analoghifi/HQ-Sub/docs/german uncorrected/SUBS-0.png

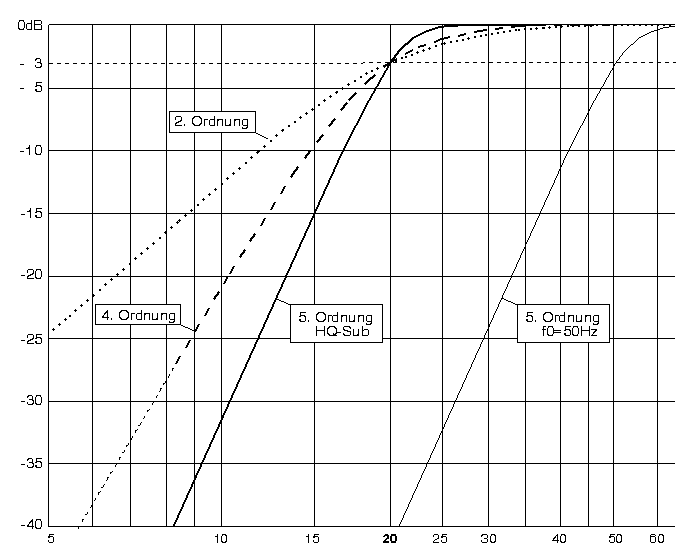
docs/german uncorrected/SUBS-0.png
