analoghifi/HQ-Sub/docs/german uncorrected/SUBS-10.png

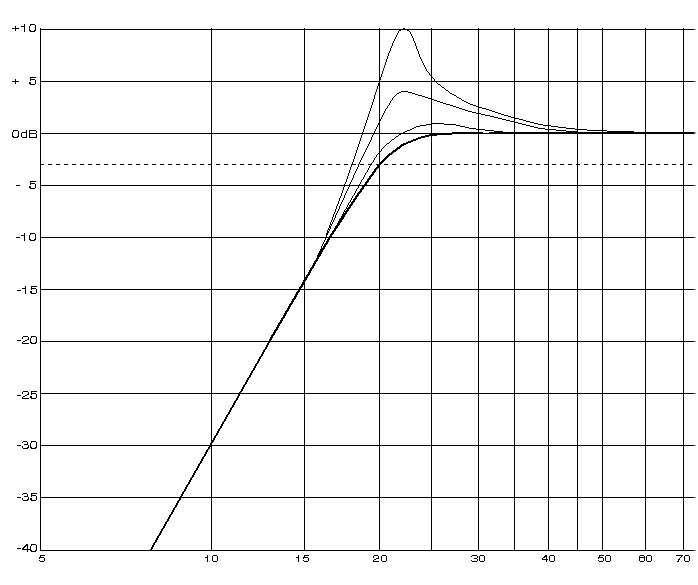
docs/german uncorrected/SUBS-10.png
