analoghifi/HQ-Sub/hardware/HQ-Sub_bottom.jpg

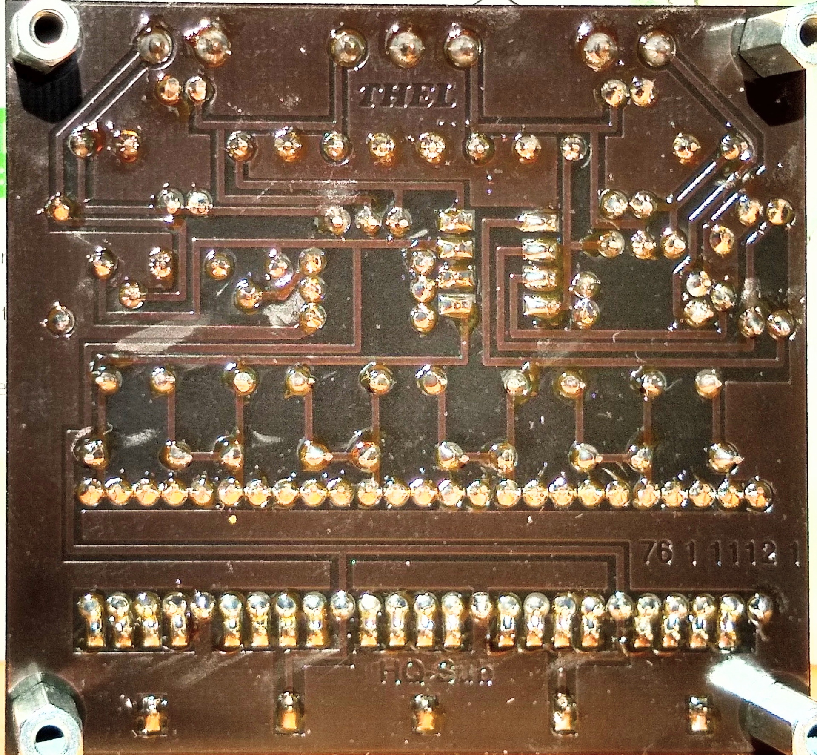
hardware/HQ-Sub_bottom.jpg
