analoghifi/HQ-Sub/hardware/HQ-Sub_Top (2).jpg

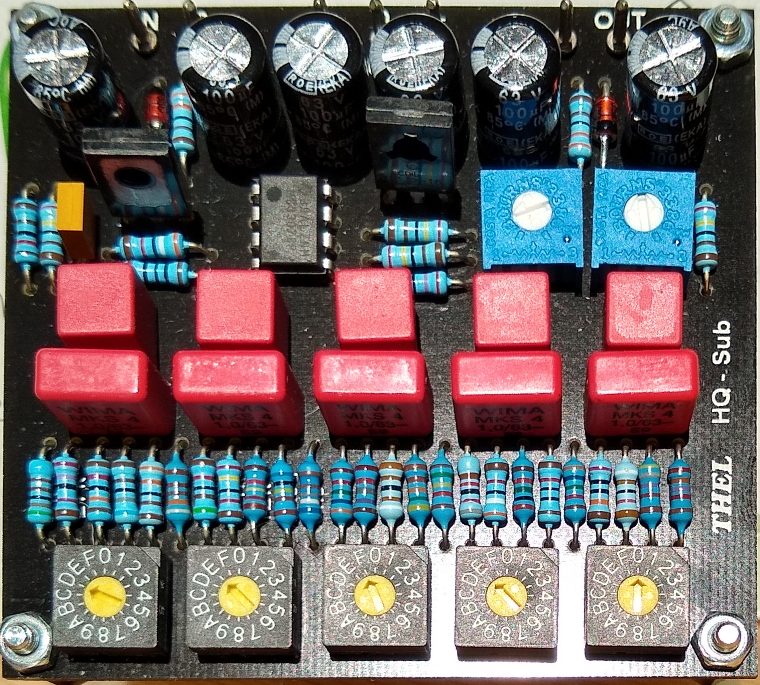
hardware/HQ-Sub_Top (2).jpg
