analoghifi/HQ-Sub/hardware/HQ-Sub_Top (3).jpg

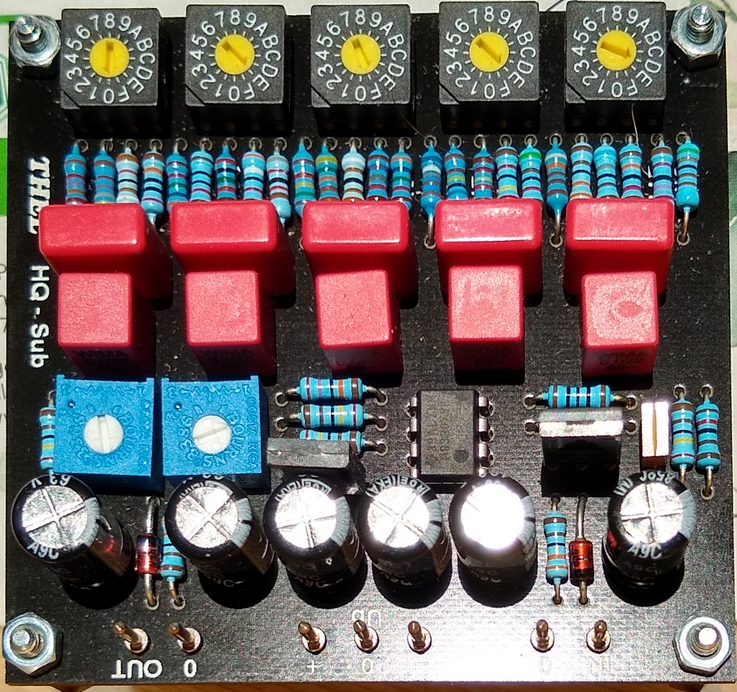
hardware/HQ-Sub_Top (3).jpg
