analoghifi/HQ-Sub/hardware/HQ-Sub_Top (4).jpg

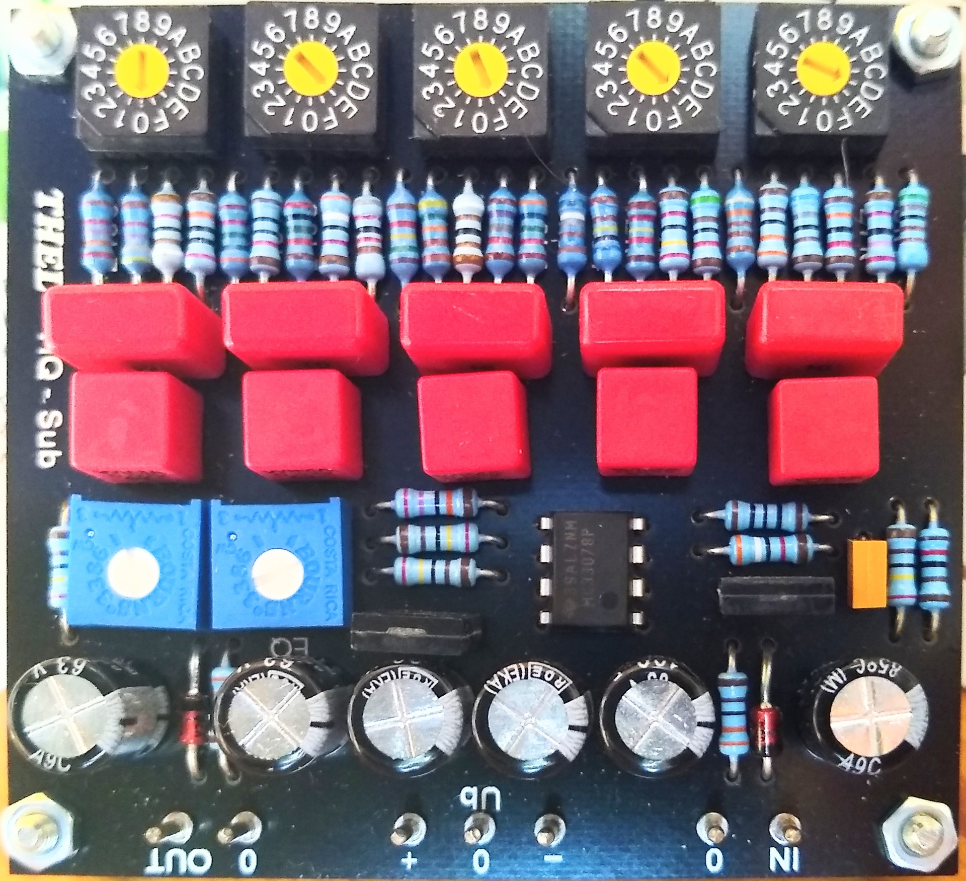
hardware/HQ-Sub_Top (4).jpg
