analoghifi/HQ-Sub/hardware/KiCad/original/HQ-Sub_original_1Layer_THT__3D_big_MKP_caps.jpg

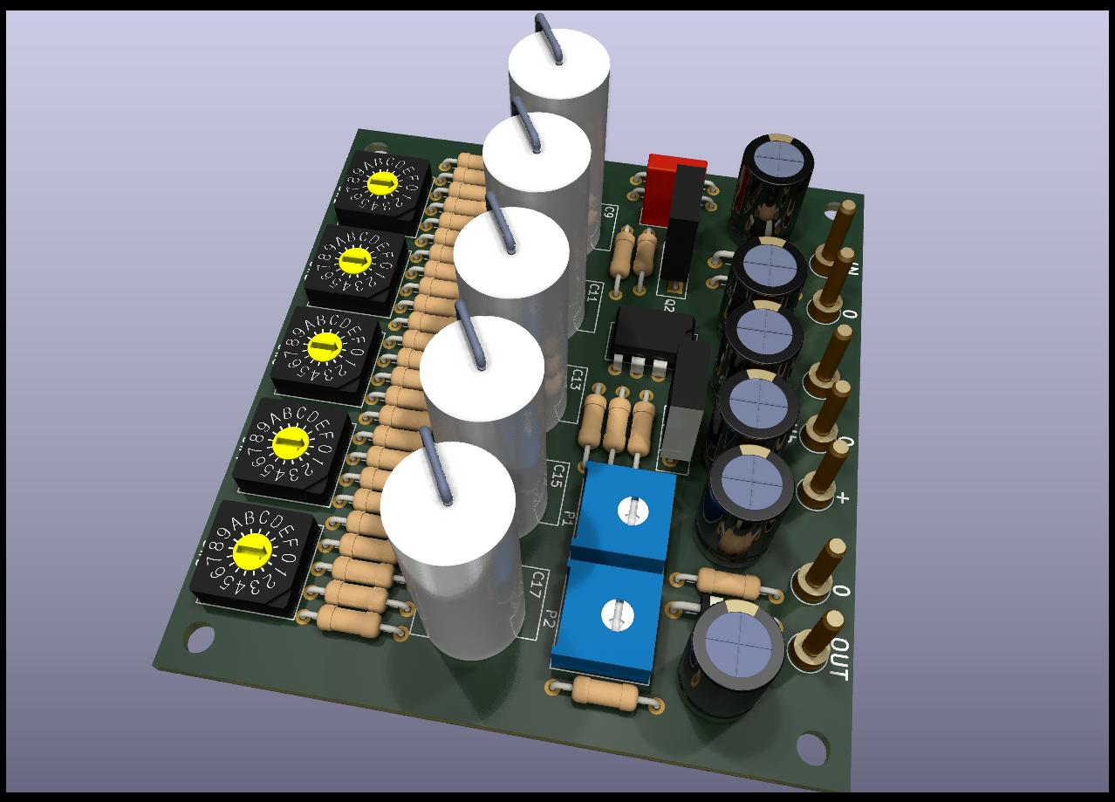
hardware/KiCad/original/HQ-Sub_original_1Layer_THT__3D_big_MKP_caps.jpg
