analoghifi/HQ-Sub/hardware/KiCad/original/HQ-Sub_original_1Layer_THT__top.png

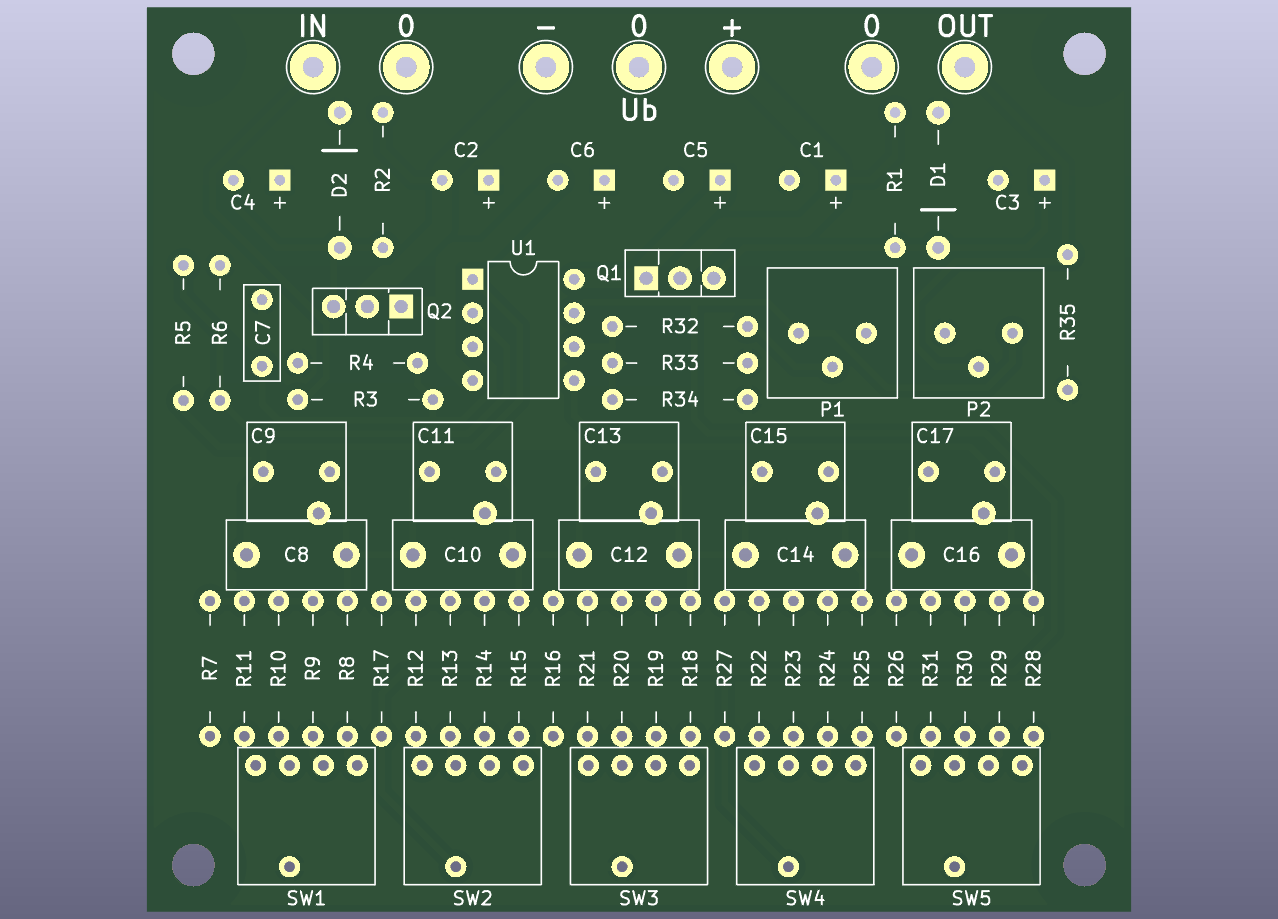
hardware/KiCad/original/HQ-Sub_original_1Layer_THT__top.png
